trinhgiahuy/OpenKinTest/paperSource/onlyHR_Subj9.jpg

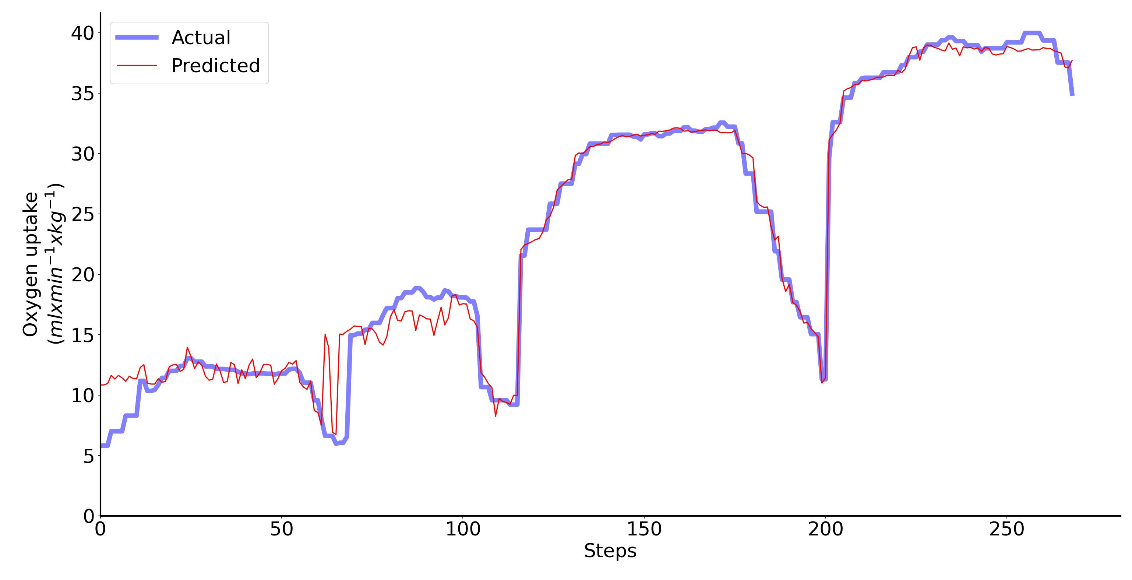
paperSource/onlyHR_Subj9.jpg
