trinhgiahuy/OpenKinTest/VO2-NN/1st-stage/1000pochs_Multiple_Subj_Training.jpg

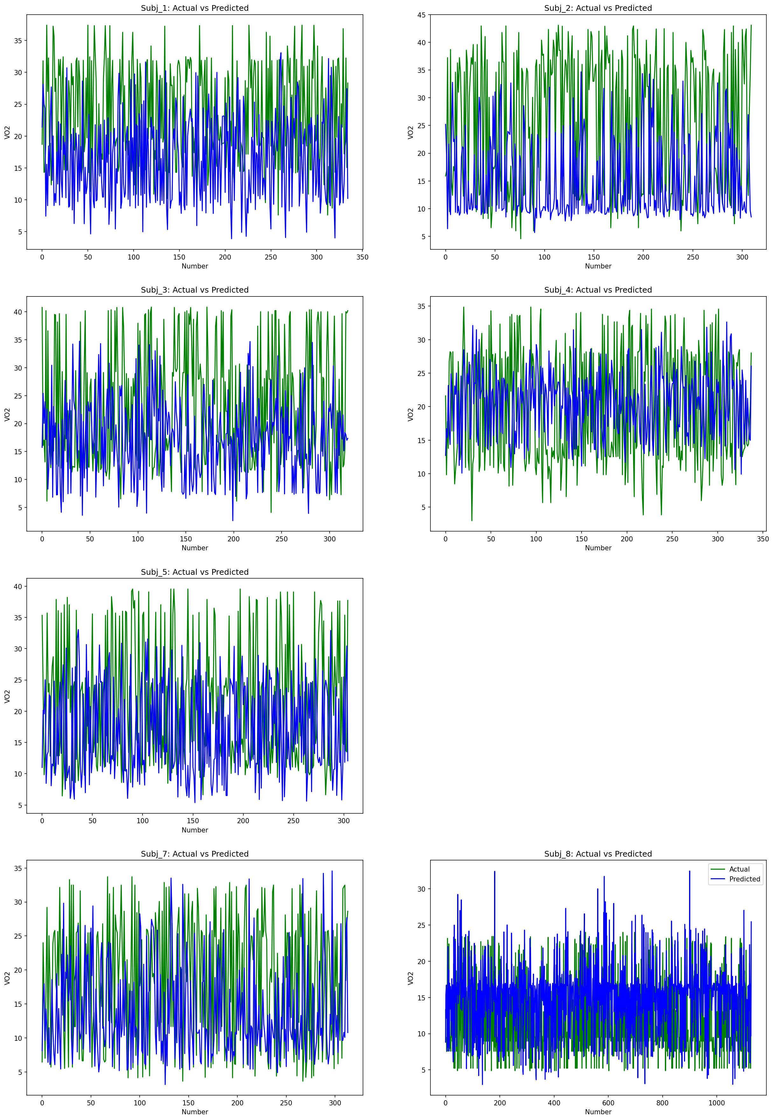
VO2-NN/1st-stage/1000pochs_Multiple_Subj_Training.jpg
