trinhgiahuy/OpenKinTest/VO2-NN/1st-stage/ideal1-pred.png

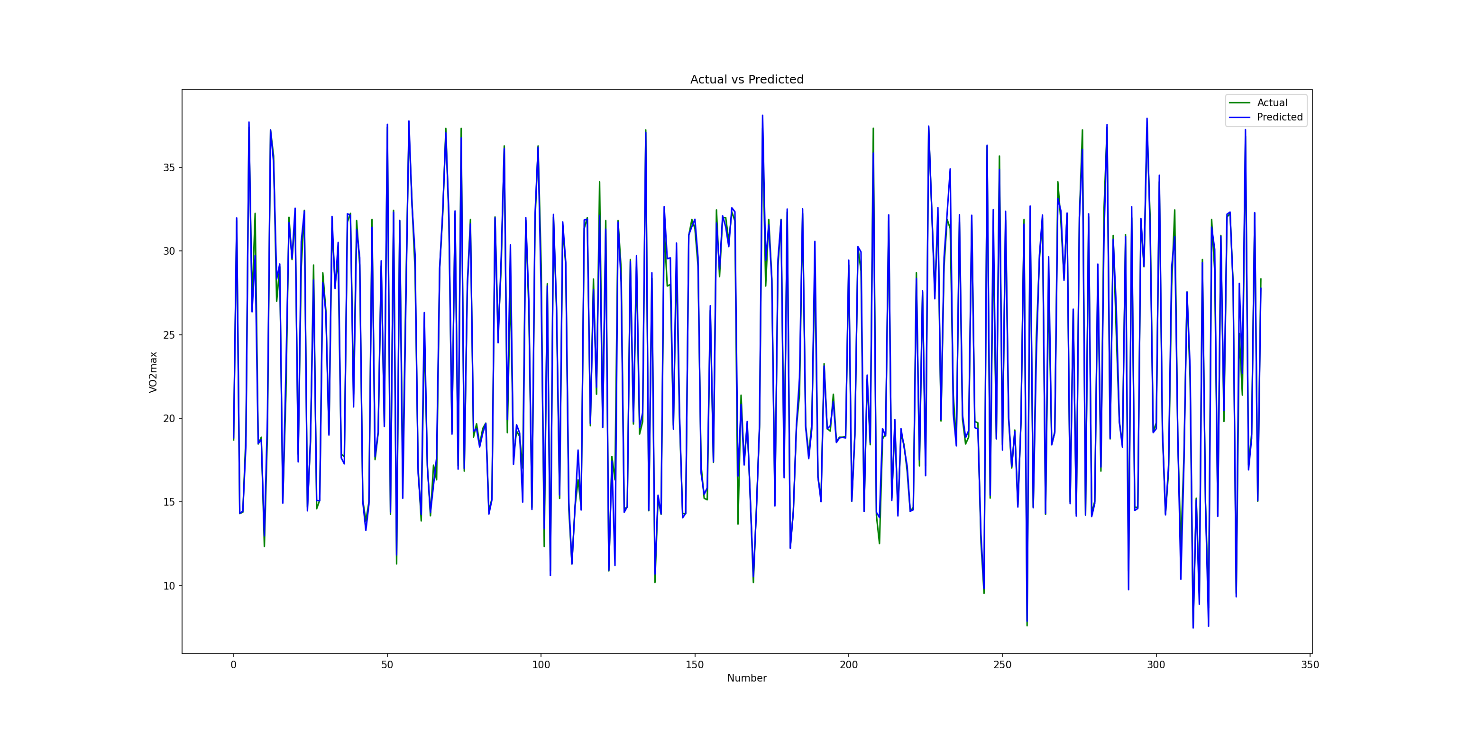
VO2-NN/1st-stage/ideal1-pred.png
