trinhgiahuy/OpenKinTest/VO2-NN/1st-stage/multiple_subject_input_pred_7.png

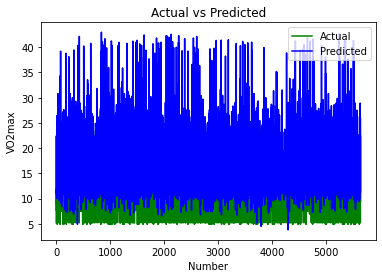
VO2-NN/1st-stage/multiple_subject_input_pred_7.png
