trinhgiahuy/OpenKinTest/VO2-NN/Model1-Trained2-ReTrani1-RePred1.png

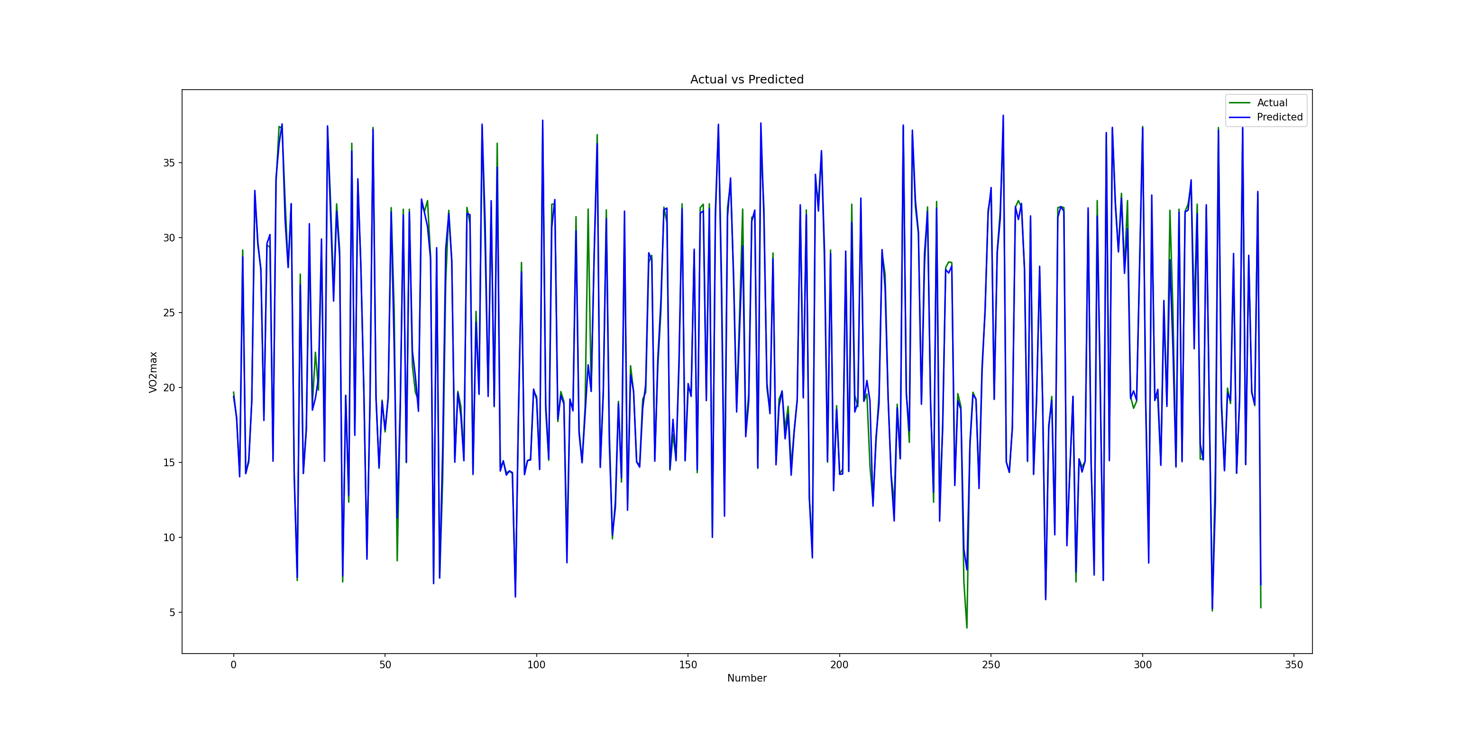
VO2-NN/Model1-Trained2-ReTrani1-RePred1.png
