trinhgiahuy/OpenKinTest/paperSource/NoHR_Subj9-1000pochs-order-100-LSTM_u-rmse1.494.jpg

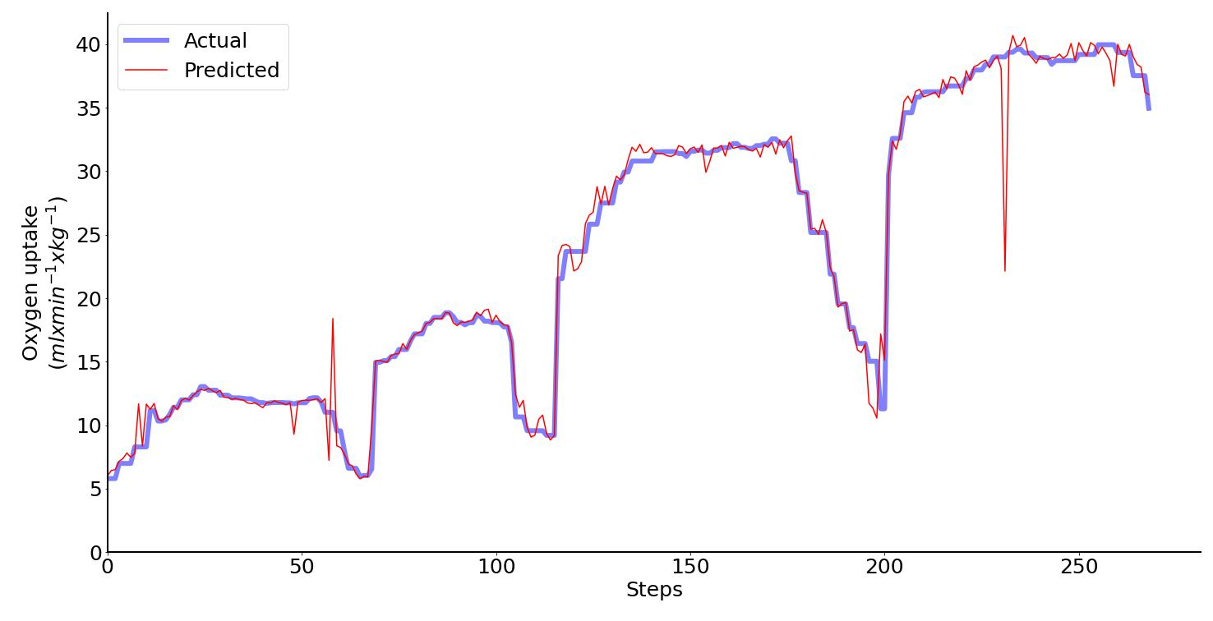
paperSource/NoHR_Subj9-1000pochs-order-100-LSTM_u-rmse1.494.jpg
