trinhgiahuy/OpenKinTest/3d/STL/rpi_case_assembly_v1_7-vectornav - rpi_blockbase_v1_7-1-1.STL

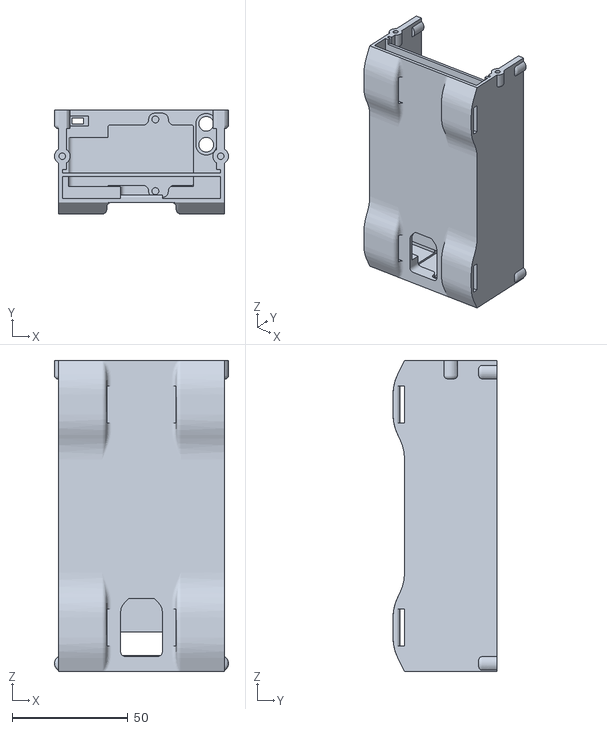
[picture p29: CAD file, 2021-05-29]
3d/STL/rpi_case_assembly_v1_7-vectornav - rpi_blockbase_v1_7-1-1.STL
75.3 x 45.0 x 134.5
