trinhgiahuy/OpenKinTest/3d/FreeCAD/pozyx_rpi_adapter_v0.4.fcstd

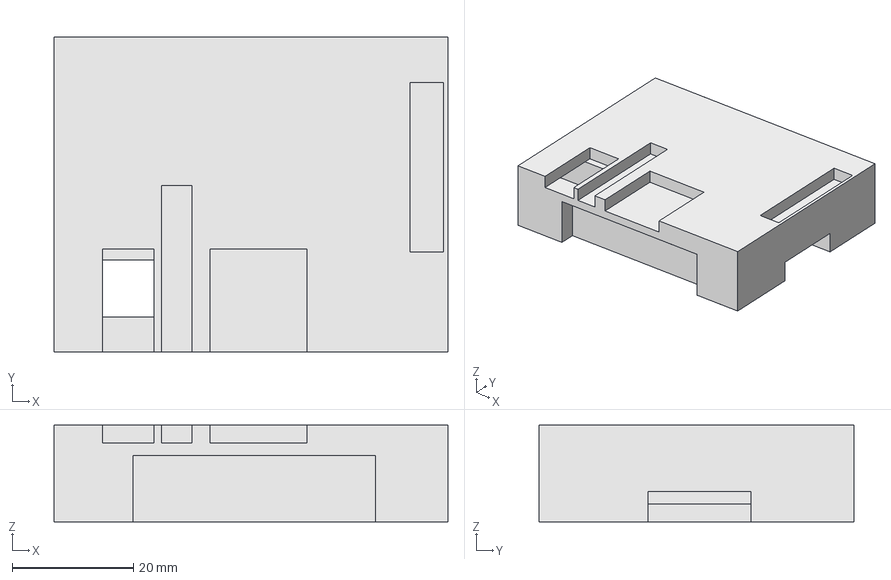
[picture p30: CAD file, 2021-05-29]
3d/FreeCAD/pozyx_rpi_adapter_v0.4.fcstd
65.0 x 52.0 x 16.0 mm
