trinhgiahuy/OpenKinTest/3d/Solidworks/gps-hole-cover.SLDPRT

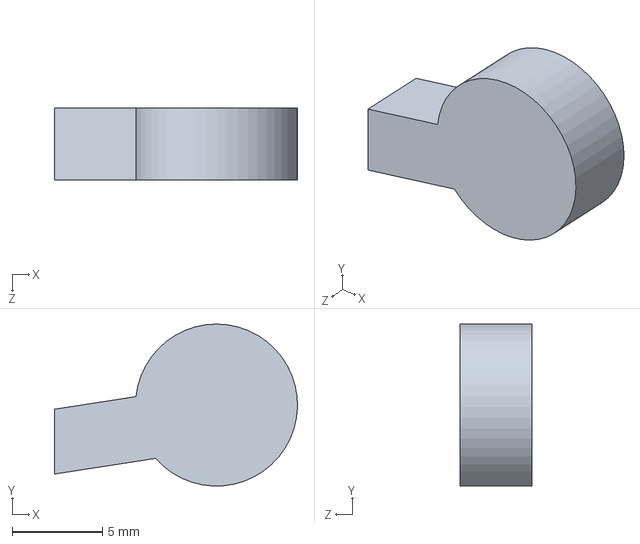
[picture p31: CAD file, 2021-05-29]
3d/Solidworks/gps-hole-cover.SLDPRT
13.5 x 8.99 x 4.00 mm
