trinhgiahuy/OpenKinTest/3d/FreeCAD/pozyx_adapter_v4.fcstd

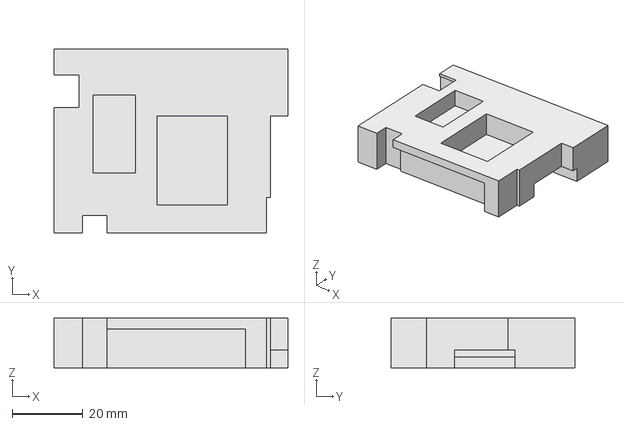
[picture p32: CAD file, 2021-05-29]
3d/FreeCAD/pozyx_adapter_v4.fcstd
66.0 x 52.0 x 14.0 mm
