trinhgiahuy/OpenKinTest/3d/MyFirstDataLoggerCase/blockbase_allholes_test2.stl

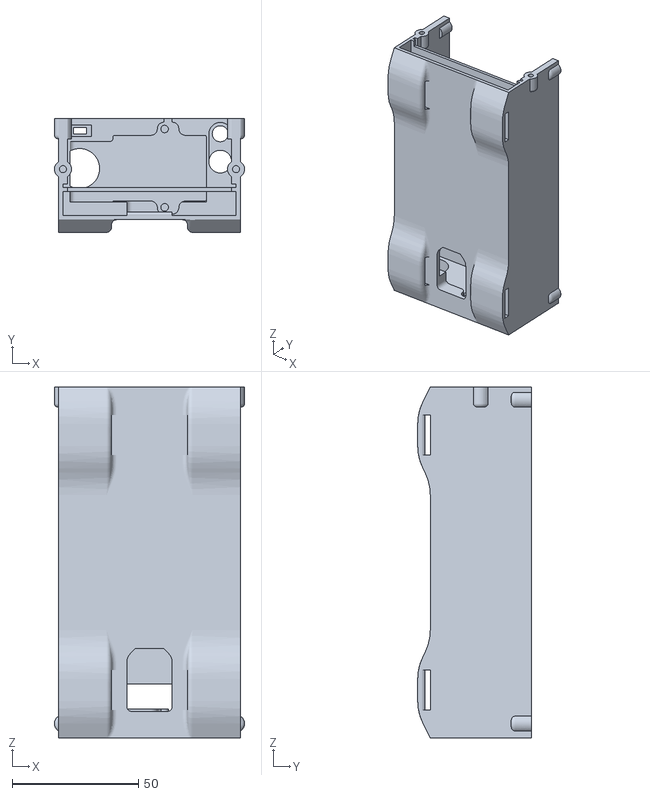
[picture p33: CAD file, 2021-11-01]
3d/MyFirstDataLoggerCase/blockbase_allholes_test2.stl
75.3 x 45.0 x 138.9
