trinhgiahuy/OpenKinTest/3d/Solidworks/minnow_blockbase_v3_5.SLDPRT

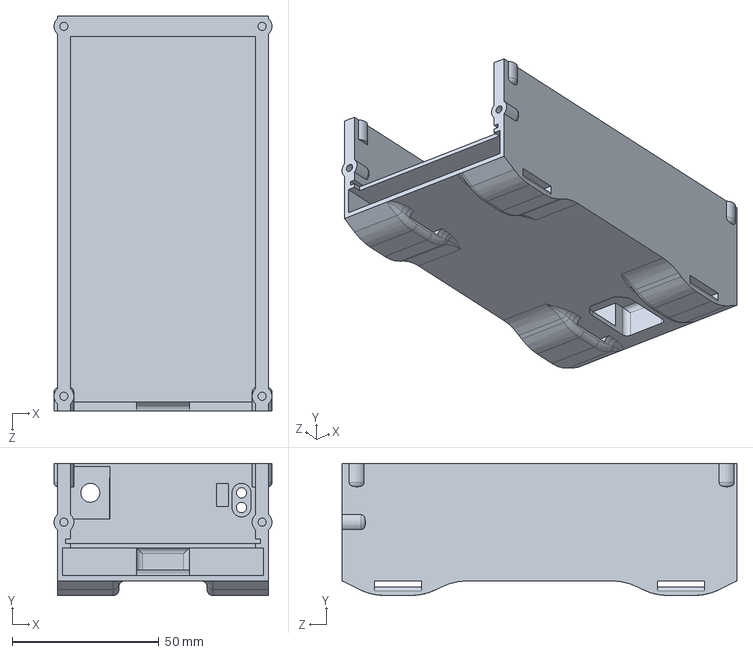
[picture p34: CAD file, 2021-05-29]
3d/Solidworks/minnow_blockbase_v3_5.SLDPRT
74.3 x 45.0 x 134.5 mm
