trinhgiahuy/OpenKinTest/3d/Solidworks/minnow_base_v3_5.SLDPRT

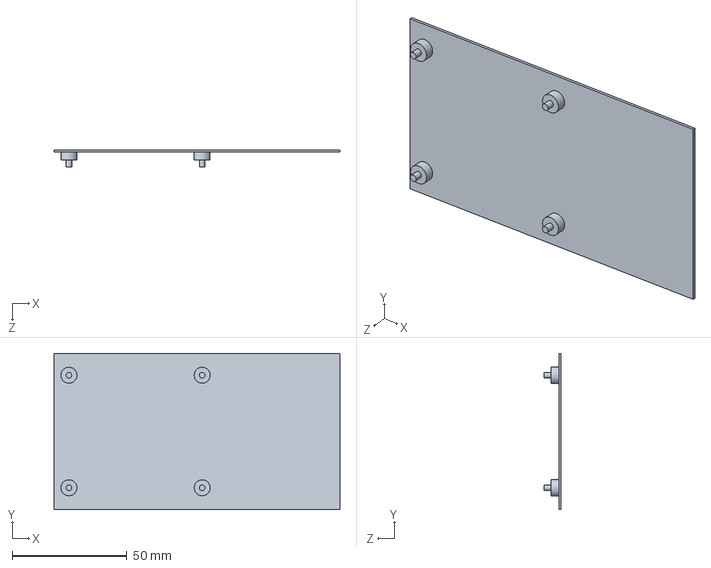
[picture p35: CAD file, 2021-05-29]
3d/Solidworks/minnow_base_v3_5.SLDPRT
124.5 x 68.0 x 7.50 mm
