trinhgiahuy/OpenKinTest/3d/Solidworks/rpi_lid2_v1_84.SLDPRT

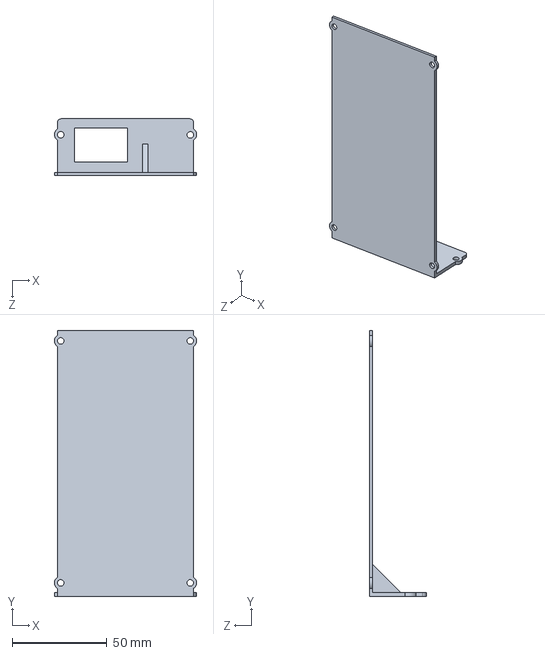
[picture p36: CAD file, 2021-05-29]
3d/Solidworks/rpi_lid2_v1_84.SLDPRT
75.3 x 140.7 x 29.9 mm
