trinhgiahuy/OpenKinTest/3d/Solidworks/rpi_base_v1_84.SLDPRT

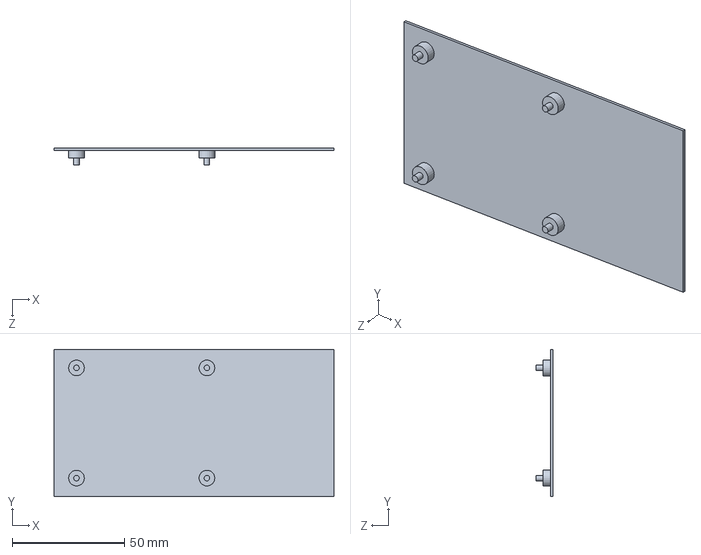
[picture p37: CAD file, 2021-05-29]
3d/Solidworks/rpi_base_v1_84.SLDPRT
124.5 x 65.5 x 7.50 mm
