trinhgiahuy/OpenKinTest/3d/Solidworks/minnow_lid_v3_5.sldprt

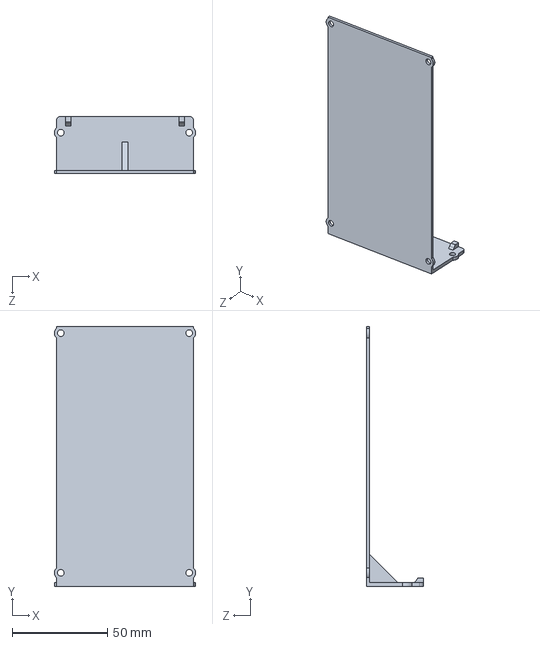
[picture p38: CAD file, 2021-05-29]
3d/Solidworks/minnow_lid_v3_5.sldprt
74.3 x 136.7 x 30.0 mm
