trinhgiahuy/OpenKinTest/1_measure_files/wHR/README.md

### This folder contain version 1 of Matlab/Python files for oxygen uptake prediction with Heart rate data
