trinhgiahuy/OpenKinTest/1_measure_files/shorter_ver/README.md

### This shorter version removes feature_OK() function as well as return step count, # windowEnd and # back
