trinhgiahuy/OpenKinTest/1_measure_files/Pavel_paper/2022-11-01_09-25-43_203130000581_LinearAccelerationTestActivity.csv

Timestamp (ms) | X: (m/s^2) | Y: (m/s^2) | Z: (m/s^2)
13382368 | -0 | 318257 | 9 | 655384 | 0 | 725051
13382378 | -0 | 236898 | 9 | 645813 | 0 | 799231
13382387 | -0 | 270399 | 9 | 621883 | 0 | 737016
13382397 | -0 | 263220 | 9 | 641026 | 0 | 760945
13382406 | -0 | 227326 | 9 | 674527 | 0 | 799231
13382416 | -0 | 282363 | 9 | 710421 | 0 | 815982
13382426 | -0 | 270399 | 9 | 710421 | 0 | 780088
13382435 | -0 | 169896 | 9 | 703242 | 0 | 729837
13382444 | -0 | 196218 | 9 | 691278 | 0 | 689158
13382454 | -0 | 193826 | 9 | 605133 | 0 | 722658
13382463 | -0 | 229719 | 9 | 588383 | 0 | 758552
13382473 | -0 | 294328 | 9 | 629062 | 0 | 813589
13382482 | -0 | 234505 | 9 | 660170 | 0 | 839911
13382492 | -0 | 155539 | 9 | 638634 | 1 | 064844
13382502 | -0 | 122038 | 9 | 645813 | 1 | 100738
13382511 | -0 | 430723 | 9 | 724778 | 0 | 801624
13382519 | -0 | 351757 | 9 | 748708 | 0 | 380472
13382529 | -0 | 050251 | 9 | 765458 | 0 | 715479
13382538 | 0 | 004786 | 9 | 523774 | 0 | 887769
13382548 | -0 | 387651 | 9 | 456773 | 0 | 629335
13382557 | -0 | 454653 | 9 | 349092 | 0 | 916484
13382567 | -0 | 404401 | 9 | 660170 | 1 | 050487
13382577 | -0 | 373294 | 9 | 696064 | 0 | 854268
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
